lologog/CubeSumo/Firmware/HardwareTest/Core/Inc/main.h

#define LUX3_Pin GPIO_PIN_0
#define LUX3_GPIO_Port GPIOA
#define LUX2_Pin GPIO_PIN_1
#define LUX2_GPIO_Port GPIOA
#define LUX4_Pin GPIO_PIN_3
#define LUX4_GPIO_Port GPIOA
#define LUX1_Pin GPIO_PIN_4
#define LUX1_GPIO_Port GPIOA
#define LED1_Pin GPIO_PIN_8
#define LED1_GPIO_Port GPIOA
#define LED3_Pin GPIO_PIN_9
#define LED3_GPIO_Port GPIOA
#define LED2_Pin GPIO_PIN_10
#define LED2_GPIO_Port GPIOA
#define BTN_Pin GPIO_PIN_11
#define BTN_GPIO_Port GPIOA
#define LED4_Pin GPIO_PIN_12
#define LED4_GPIO_Port GPIOA
#define SWDIO_Pin GPIO_PIN_13
#define SWDIO_GPIO_Port GPIOA
#define SWCLK_Pin GPIO_PIN_14
#define SWCLK_GPIO_Port GPIOA
#define LD3_Pin GPIO_PIN_3
#define LD3_GPIO_Port GPIOB
#define EN_LEFT_Pin GPIO_PIN_4
#define EN_LEFT_GPIO_Port GPIOB
#define PHASE_LEFT_Pin GPIO_PIN_5
#define PHASE_LEFT_GPIO_Port GPIOB
#define EN_RIGHT_Pin GPIO_PIN_6
#define EN_RIGHT_GPIO_Port GPIOB
#define PHASE_RIGHT_Pin GPIO_PIN_7
#define PHASE_RIGHT_GPIO_Port GPIOB
